Annie-Zhu1210/Commuta_PortableAirMonitor/Battery/battery_curve.png

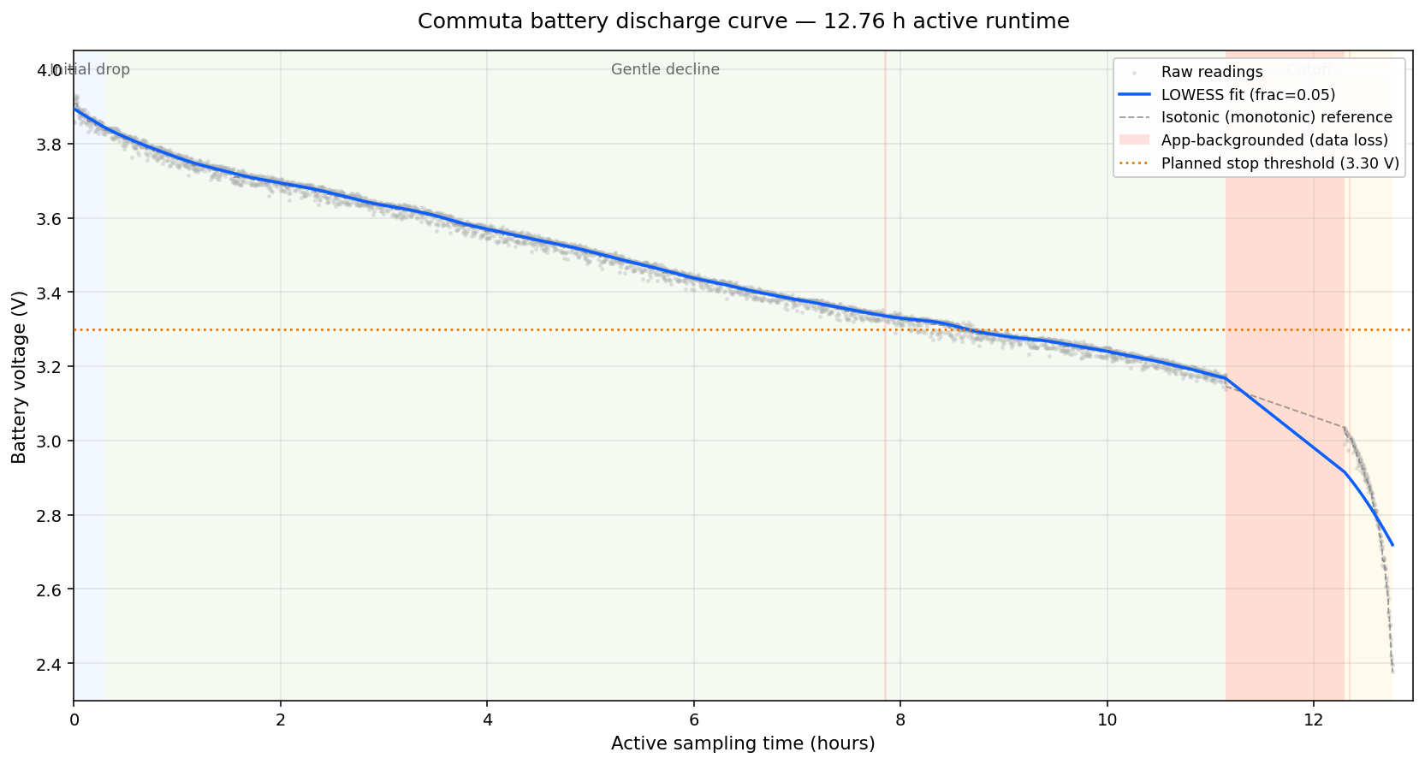
Battery/battery_curve.png
