Annie-Zhu1210/Commuta_PortableAirMonitor/Battery/voltage_percentage_curve.png

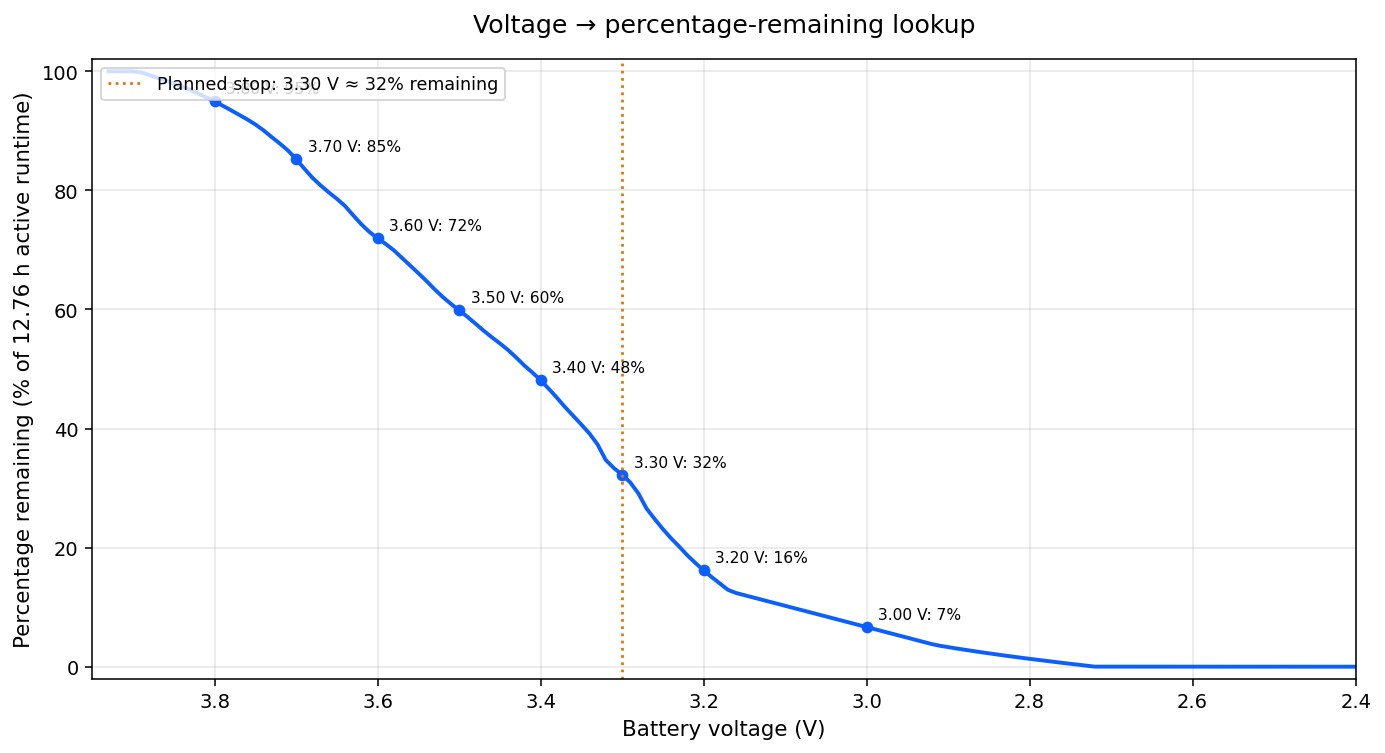
Battery/voltage_percentage_curve.png
