Annie-Zhu1210/Commuta_PortableAirMonitor/commuta_app/docs/images/herocard_red.PNG

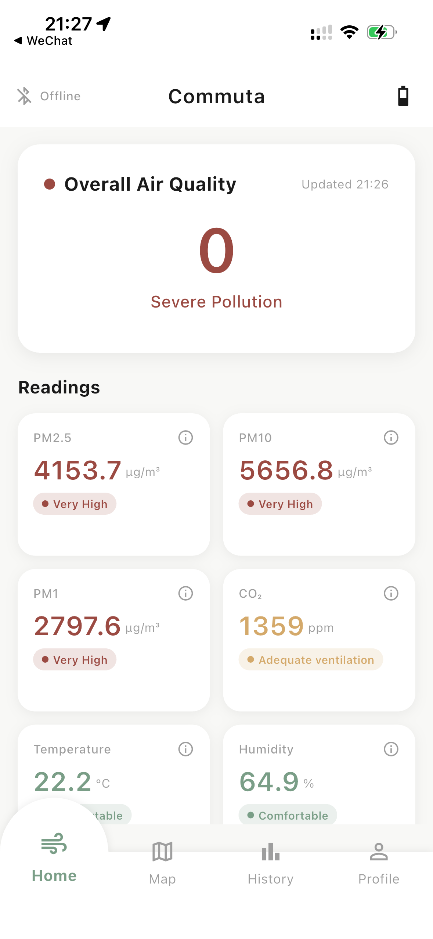
commuta_app/docs/images/herocard_red.PNG
