Annie-Zhu1210/Commuta_PortableAirMonitor/visualisation/fig_4_3_dwell_vs_pm25.png

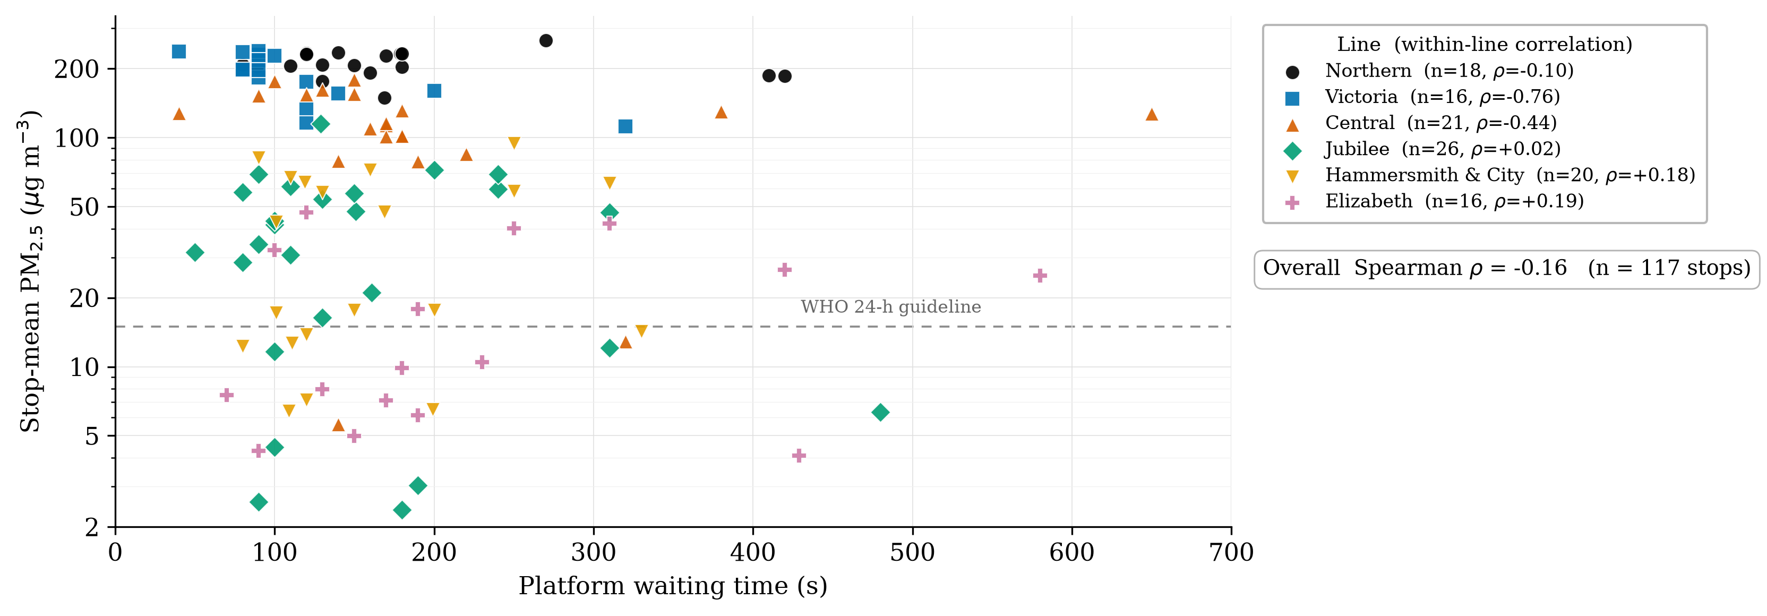
visualisation/fig_4_3_dwell_vs_pm25.png
