Annie-Zhu1210/Commuta_PortableAirMonitor/visualisation/figures/commuta_pm25_co2.png

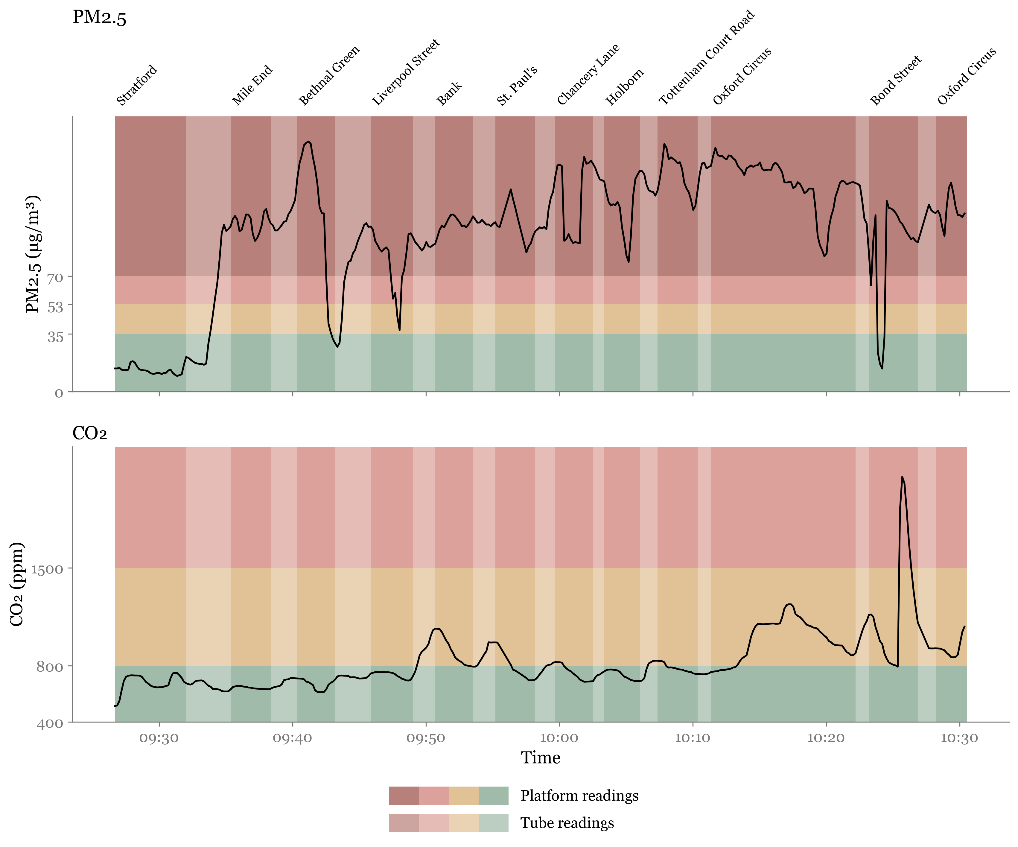
visualisation/figures/commuta_pm25_co2.png
