Annie-Zhu1210/Commuta_PortableAirMonitor/visualisation/figures/elizabeth_within_journey.png

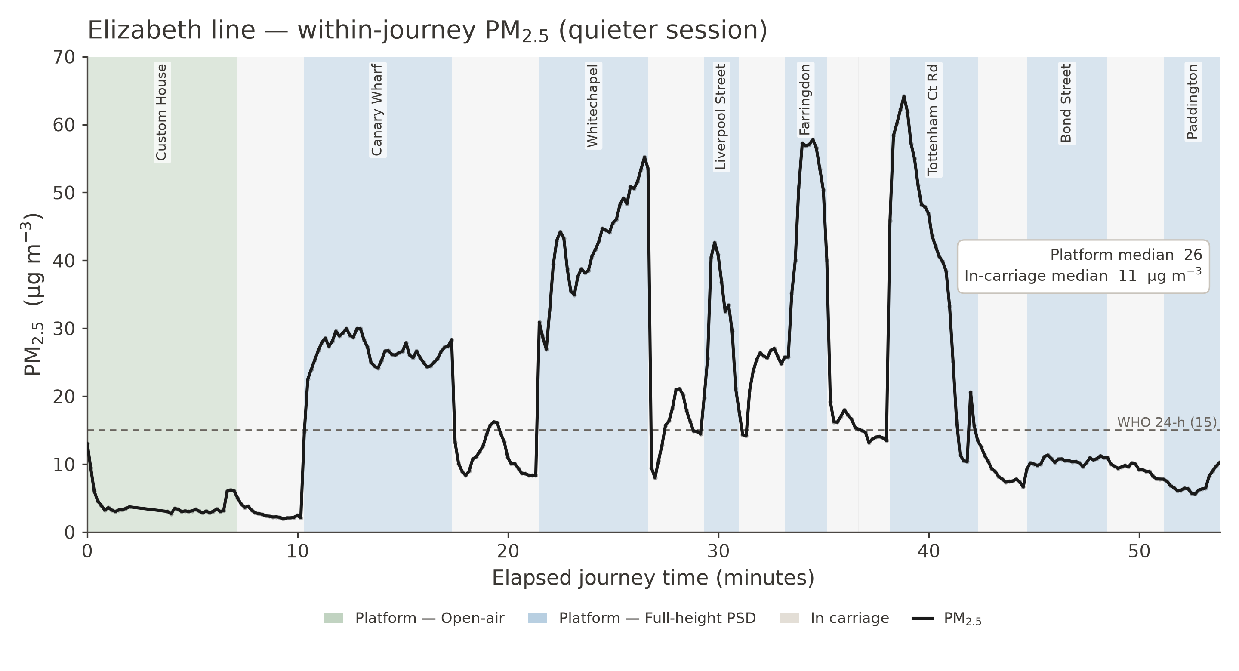
visualisation/figures/elizabeth_within_journey.png
