Annie-Zhu1210/Commuta_PortableAirMonitor/visualisation/figures/elizabeth_within_journey_busier.png

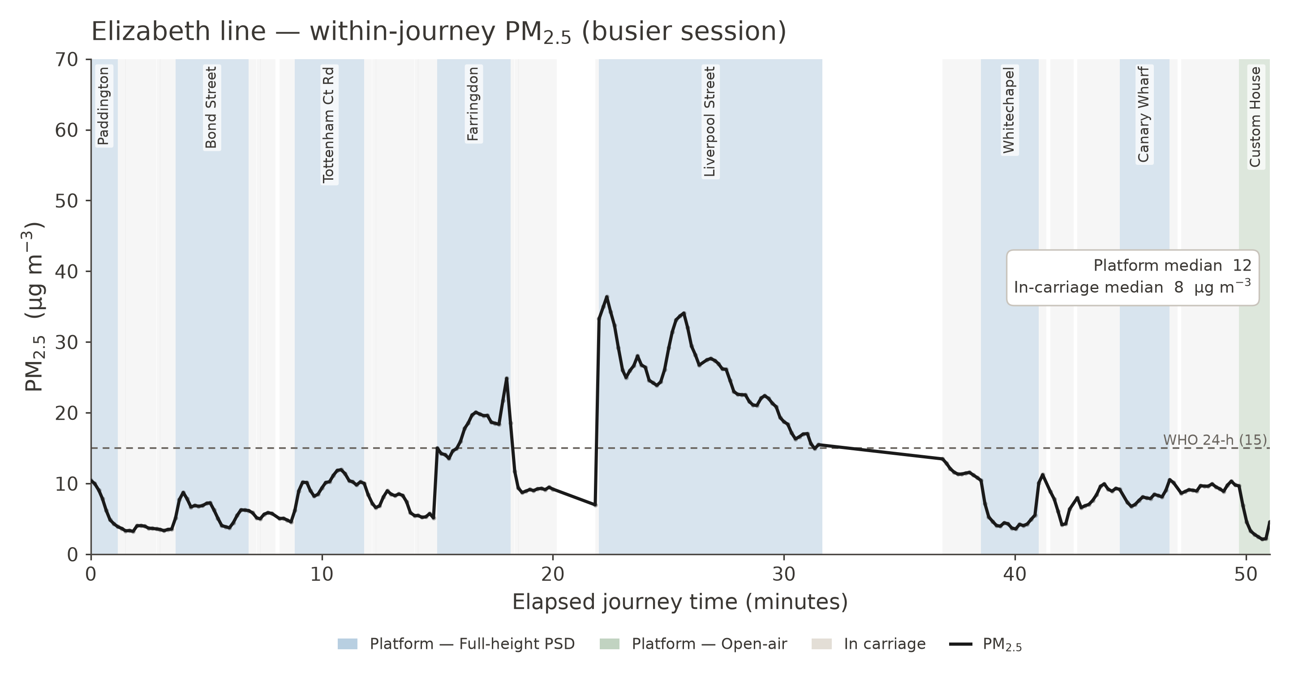
visualisation/figures/elizabeth_within_journey_busier.png
