Annie-Zhu1210/Commuta_PortableAirMonitor/visualisation/figures/fig_platform_mode.png

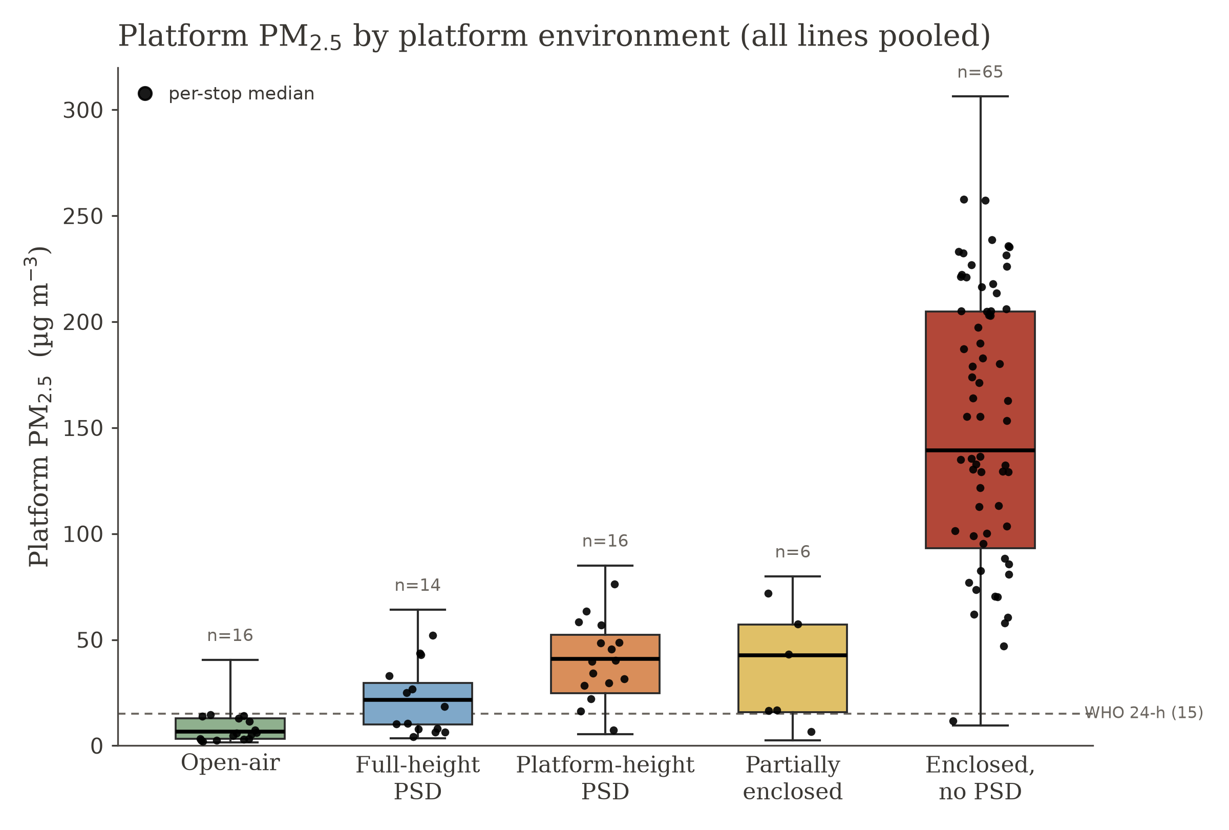
visualisation/figures/fig_platform_mode.png
