Annie-Zhu1210/Commuta_PortableAirMonitor/visualisation/figures/Jubilee_per_station.png

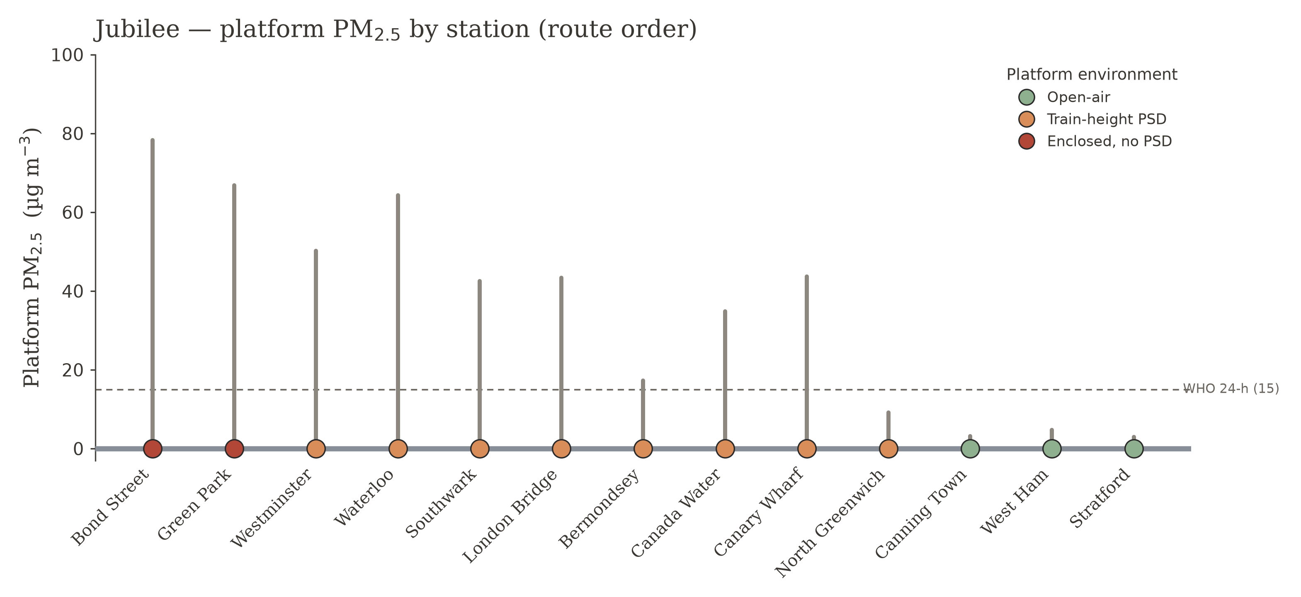
visualisation/figures/Jubilee_per_station.png
