Annie-Zhu1210/Commuta_PortableAirMonitor/test_SPS30/Breadboard.jpg

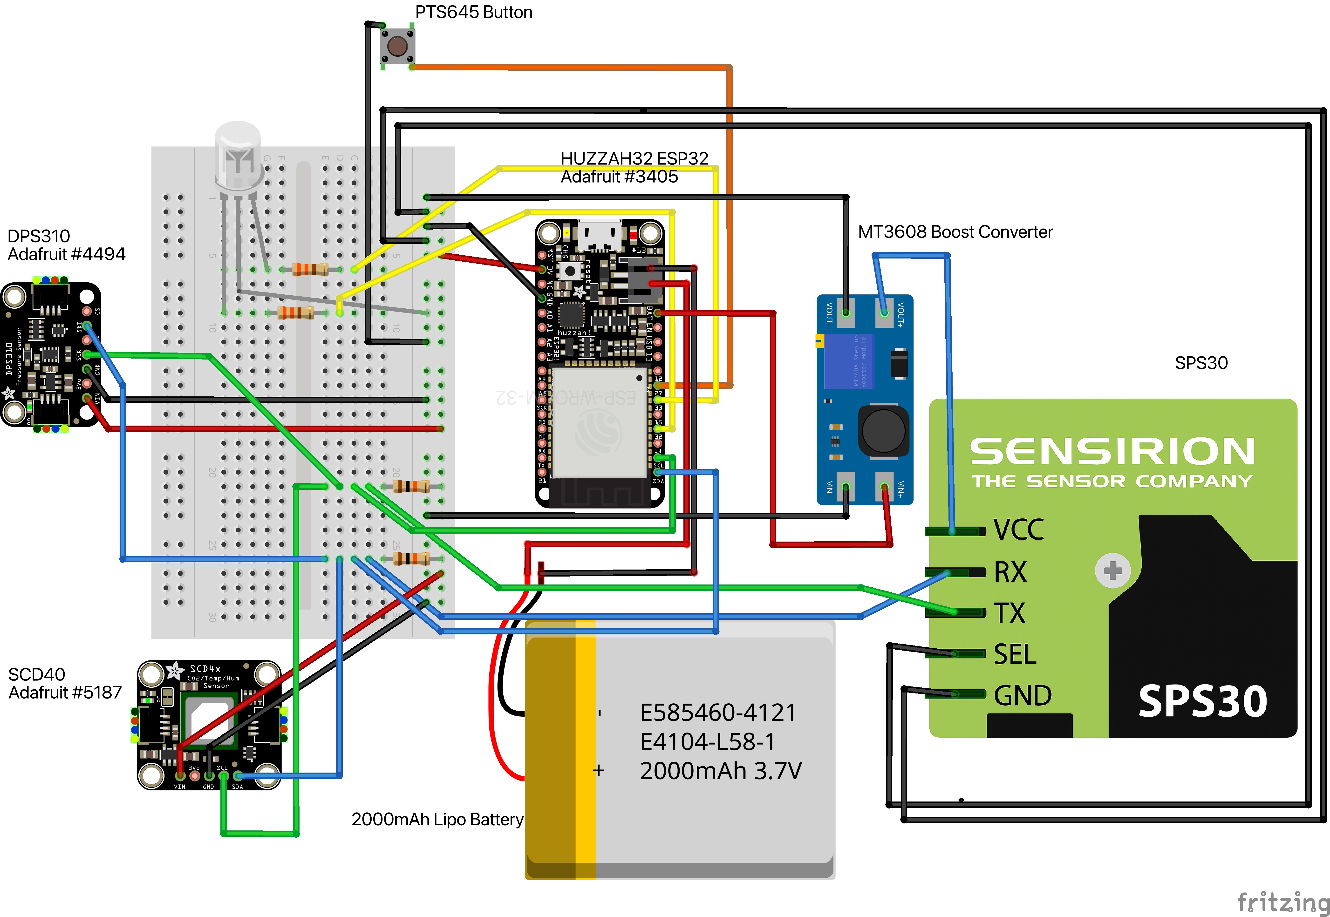
test_SPS30/Breadboard.jpg
